SanPollo/PCWGotekMod/images/photo01.jpg

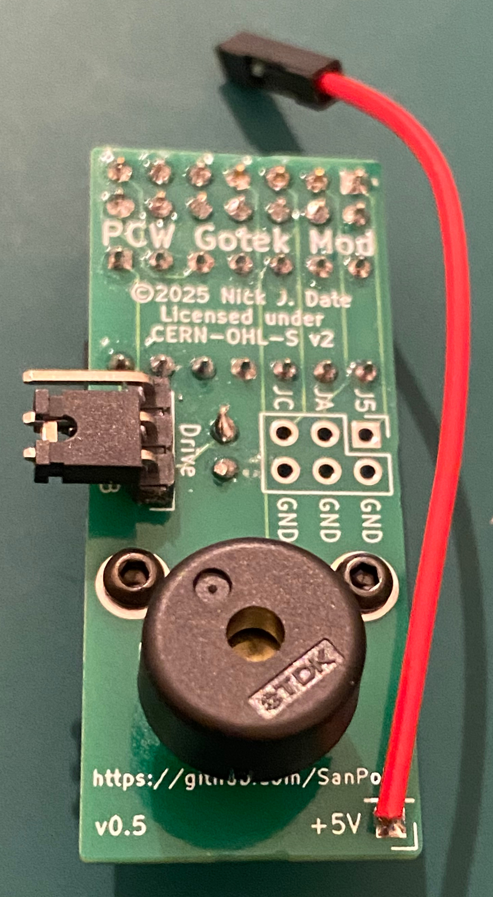
images/photo01.jpg
