SanPollo/PCWGotekMod/schematics/PCWGotekMod0.6.kicad_sch

## KiCad design schematics/PCWGotekMod0.6.kicad_sch (2025-09-28)

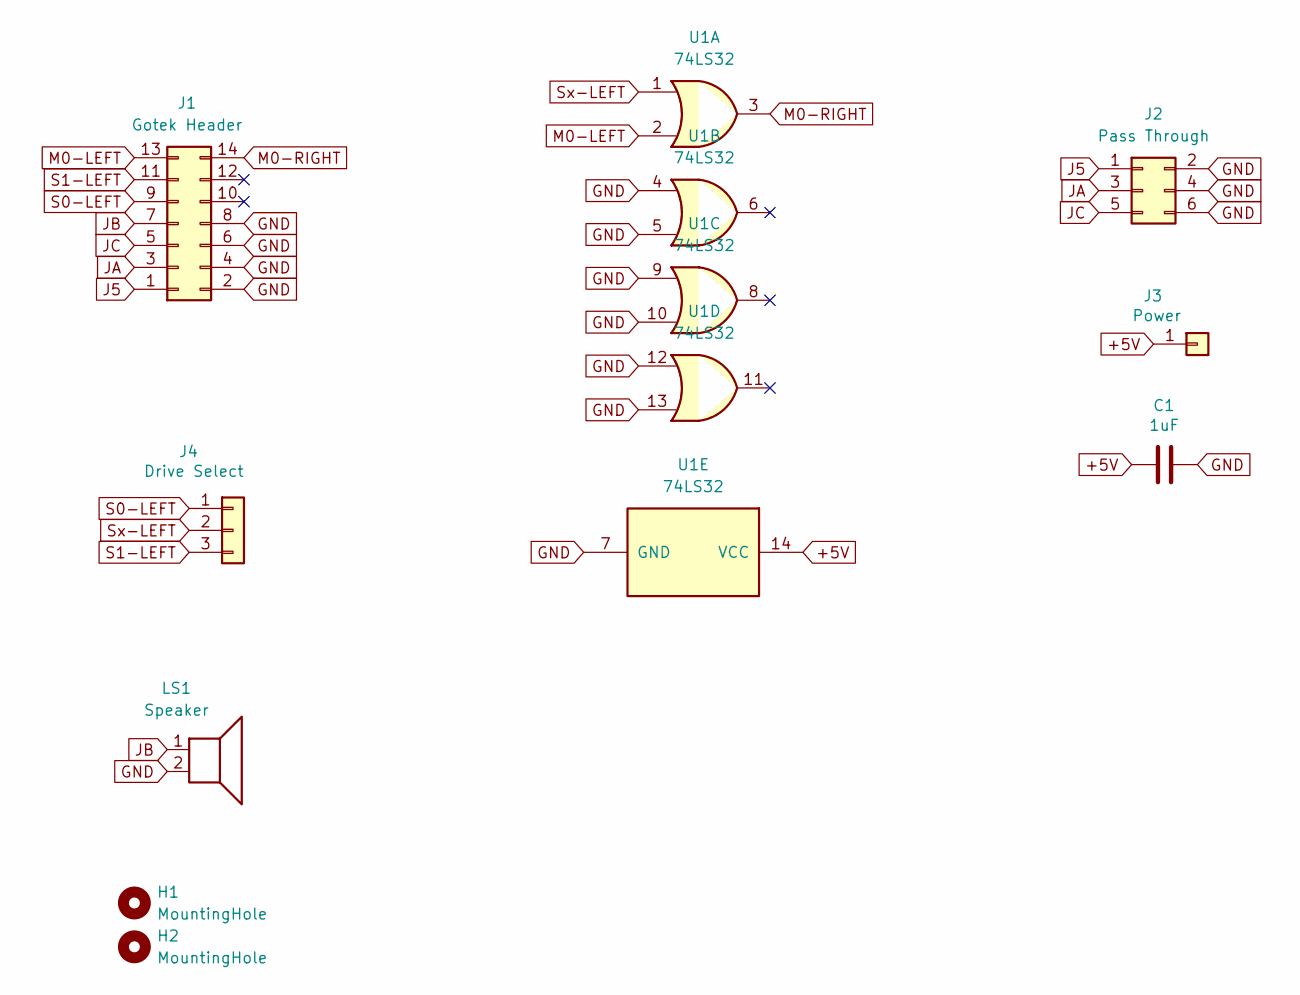
[picture p4: schematic PCWGotekMod0.6.kicad_sch]

Parts:
C1: 1uF; C_Disc_D3.0mm_W2.0mm_P2.50mm
H1, H2: MountingHole; MountingHole_2.2mm_M2_Pad
J1: Gotek Header; PinSocket_2x07_P2.54mm_Vertical
J2: Pass Through; PinHeader_2x03_P2.54mm_Vertical
J3: Power; PinHeader_1x01_P2.54mm_Vertical
J4: Drive Select; PinHeader_1x03_P2.54mm_Vertical
LS1: Speaker; Buzzer_12x9.5RM7.6
U1: 74LS32; DIP-14_W7.62mm

Connections:
+5V: C1.1, J3.1, U1.14 (VCC)
GND: C1.2, J1.2, J1.4, J1.6, J1.8, J2.2, J2.4, J2.6, LS1.2, U1.4, U1.5, U1.7 (GND), U1.9, U1.10, U1.12, U1.13
J5: J1.1, J2.1
JA: J1.3, J2.3
JB: J1.7, LS1.1
JC: J1.5, J2.5
M0-LEFT: J1.13, U1.2
M0-RIGHT: J1.14, U1.3
S0-LEFT: J1.9, J4.1
S1-LEFT: J1.11, J4.3
Sx-LEFT: J4.2, U1.1
